NathanSchenk/OmniRef/PDFs/OmniRef-F.Cu.pdf

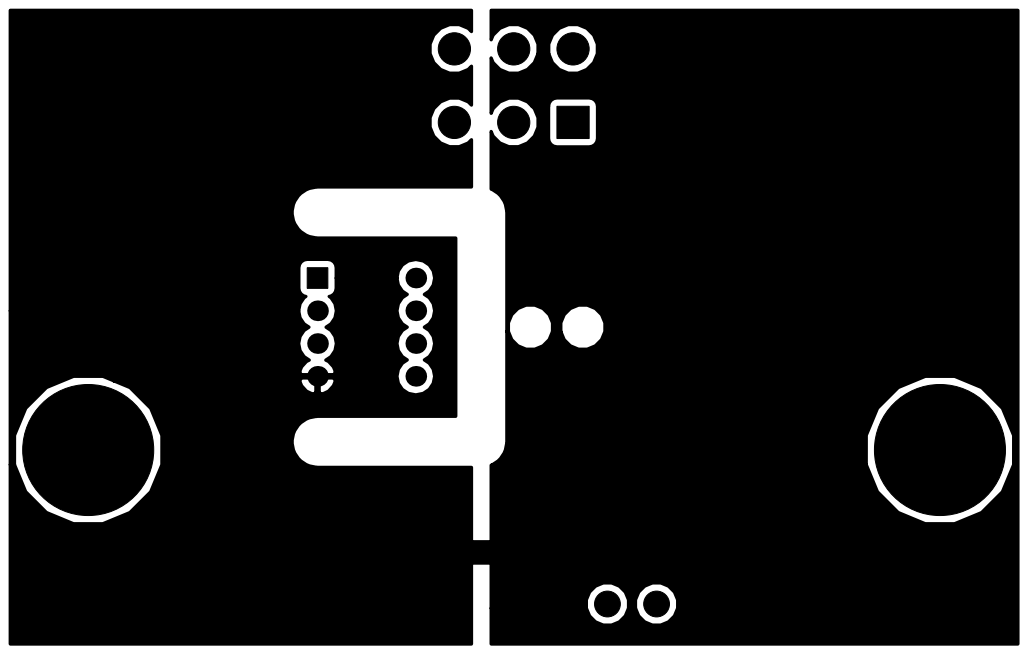
[picture p19: page 1]
