NathanSchenk/OmniRef/PDFs/OmniRef-F.Fab.pdf

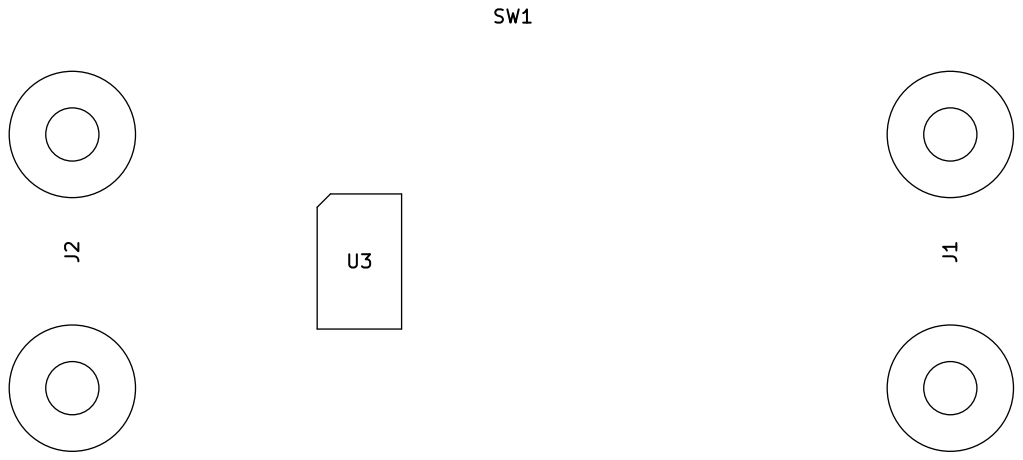
[picture p20: page 1]
