NathanSchenk/OmniRef/PDFs/OmniRef-F.Mask.pdf

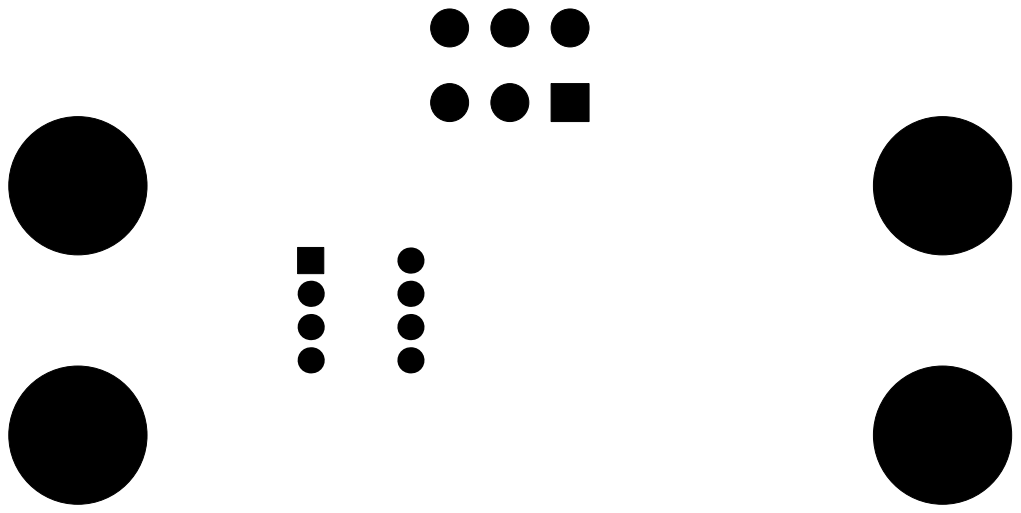
[picture p21: page 1]
