NathanSchenk/OmniRef/PDFs/OmniRef-F.SilkS.pdf

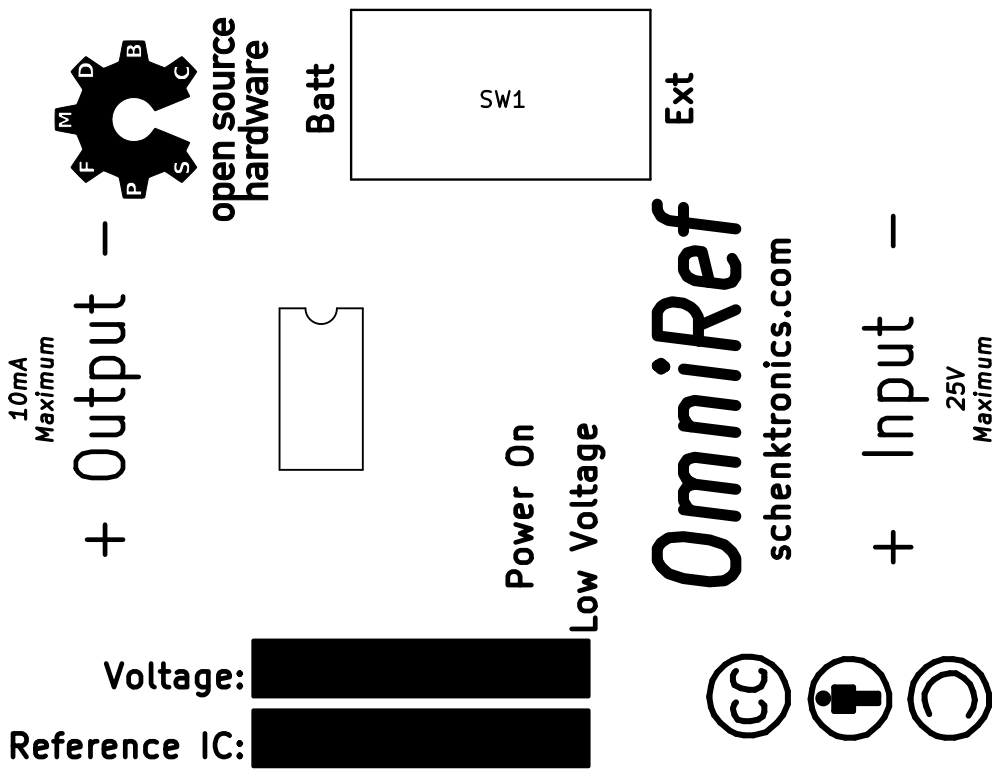
[picture p22: page 1]
